dfd/angry_squealing_duck/kicad/breadboard/02_input_buffer.png

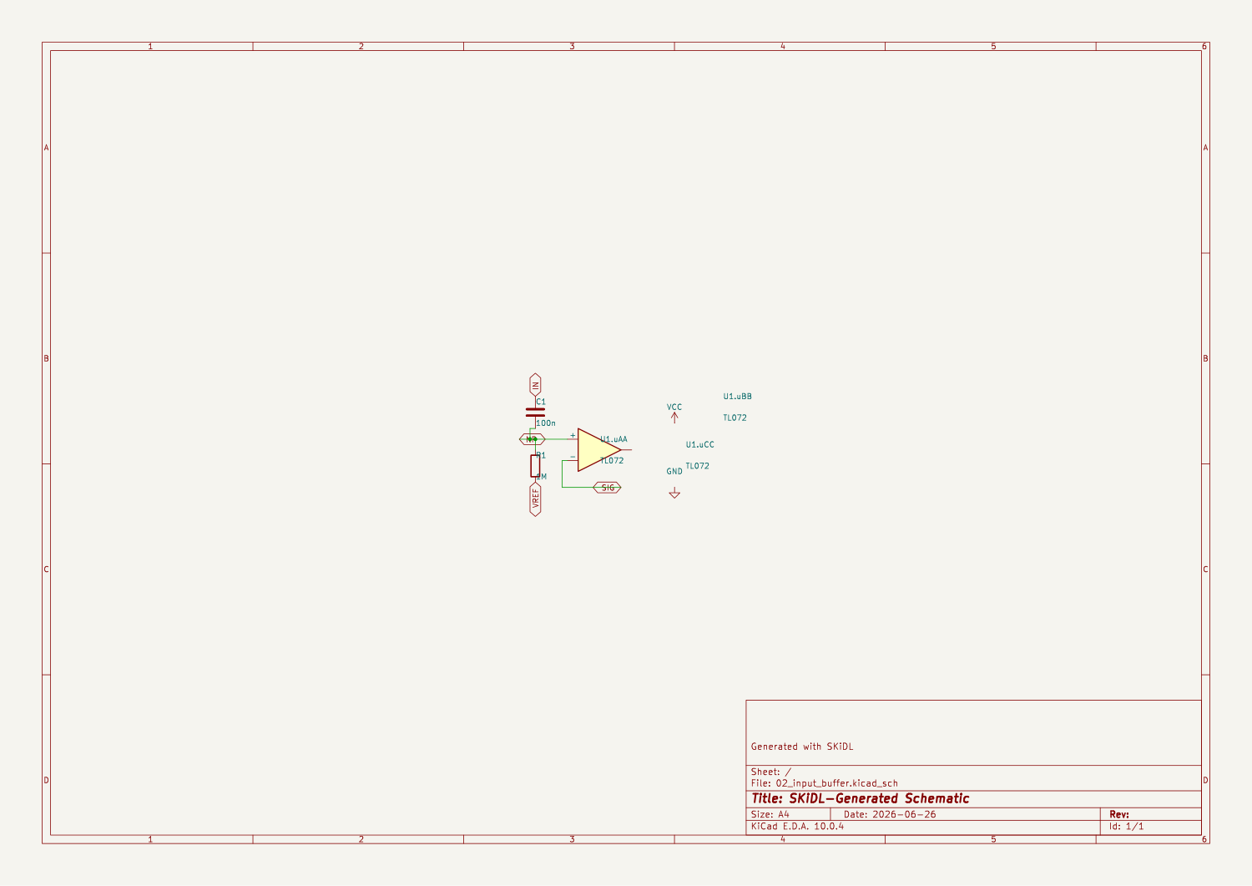
kicad/breadboard/02_input_buffer.png
