dfd/angry_squealing_duck/kicad/breadboard/05_envelope.png

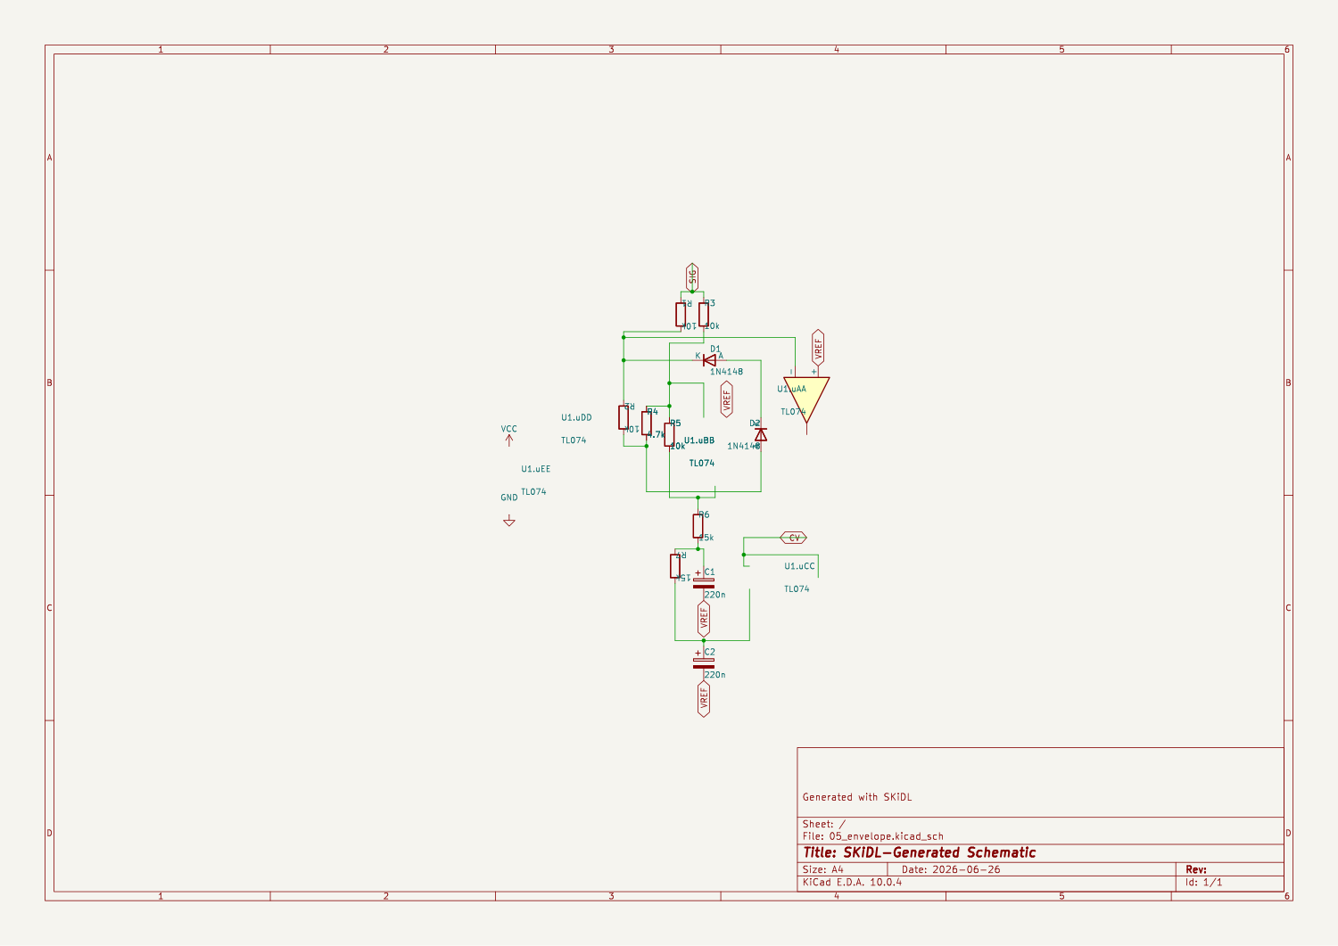
kicad/breadboard/05_envelope.png
