dfd/angry_squealing_duck/kicad/breadboard/06_quack_vtoi.png

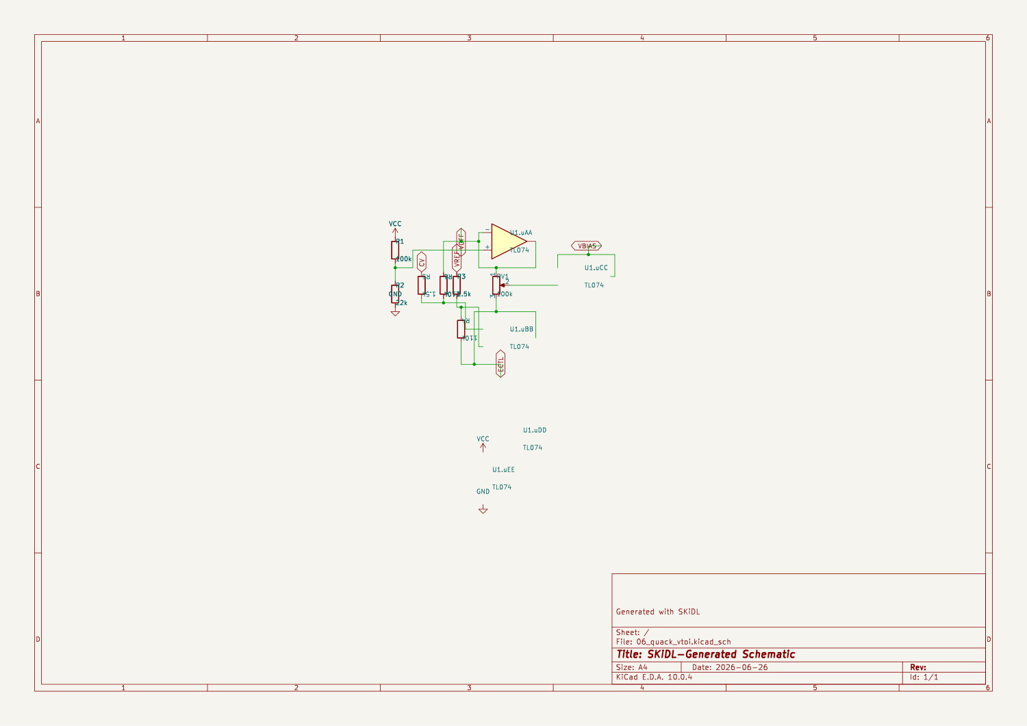
kicad/breadboard/06_quack_vtoi.png
