dfd/angry_squealing_duck/kicad/duck_place.png

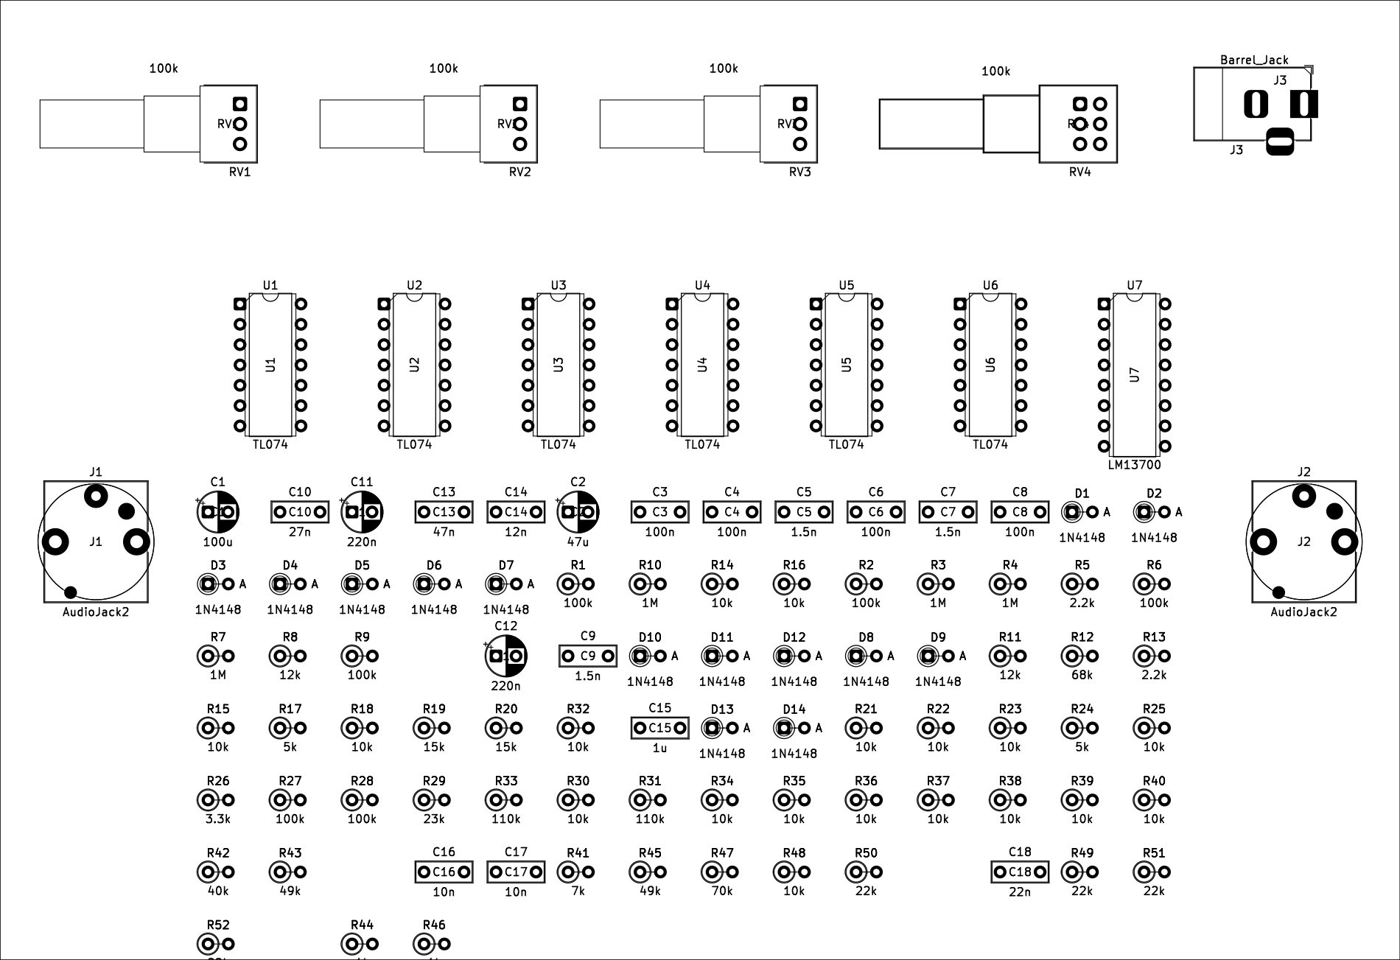
kicad/duck_place.png
