dfd/angry_squealing_duck/spice/blocks/vcf.cir

* ---------------------------------------------------------------------------
* vcf - voltage-controlled state-variable band-pass (Q-Tron core, behavioral)
*
* Pins:  in out gc vref vp vn      params: quack=1
*   gc : GROUND-referenced cutoff control (>=0; 0 = parked). Generated from the
*        envelope by the integration stage (gc = max(cv - vref, 0)).
*
* Chamberlin state-variable loop, band-pass tap:
*   hp = in - lp - d*bp        (all relative to vref)
*   bp = (w0/s) hp             (gm-C integrator 1)
*   lp = (w0/s) bp             (gm-C integrator 2)
* The state-variable loop gives all three responses at once:
*   bp = w0*s/(s^2+d*w0*s+w0^2)  hp = s^2/(...)  lp = w0^2/(...)
* Q-Tron-style mode is a weighted blend of the taps (wlp/wbp/whp), default = BP.
* HP/mixed cut the fundamental below the swept corner -> octave more apparent.
*
* Quack ganged control:
*   - sweep depth (drive): passed to the integrators (w0 swept by gc)
*   - resonance (Q):       Q = 0.7 + 2.8*quack (damping d = 1/Q), so Q ramps
*     LINEARLY 0.7 (CCW, off) -> 3.5 (CW). Linear-in-Q spreads the quack evenly
*     across the knob (vs 1/d which crammed it all at the top and hit Q~10, which
*     buried the octave); 3.5 is a strong-but-musical max that keeps the octave present.
* So Quack CCW = parked, low-Q (effectively off); CW = strong resonant sweep.
* ---------------------------------------------------------------------------
.subckt vcf in out gc vref vp vn params: quack=1 wlp=0 wbp=1 whp=0
* summer -> high-pass state (ideal summing node, referenced to vref)
Bhp hp vref V = (V(in)-V(vref)) - (V(lp)-V(vref)) - (1/(0.7+2.8*quack))*(V(bp)-V(vref))
* two voltage-controlled integrators -> band-pass (bp) and low-pass (lp) taps
Xi1 hp bp gc vref gmint quack={quack}
Xi2 bp lp gc vref gmint quack={quack}
* mode = weighted blend of LP/BP/HP taps (relative to vref)
Bmix mo vref V = wlp*(V(lp)-V(vref)) + wbp*(V(bp)-V(vref)) + whp*(V(hp)-V(vref))
* buffer so downstream loads don't disturb the filter state
Xob mo out out vp vn opamp
.ends vcf
