dfd/angry_squealing_duck/OUT: Pin U1/6/-,-,p7514962063015773255,p6/INPUT, Pin U1/7/,p3768724659903456224,p7/OUTPUT/08_output.kicad_sch

## KiCad design OUT: Pin U1/6/-,-,p7514962063015773255,p6/INPUT, Pin U1/7/,p3768724659903456224,p7/OUTPUT/08_output.kicad_sch (2026-06-26)

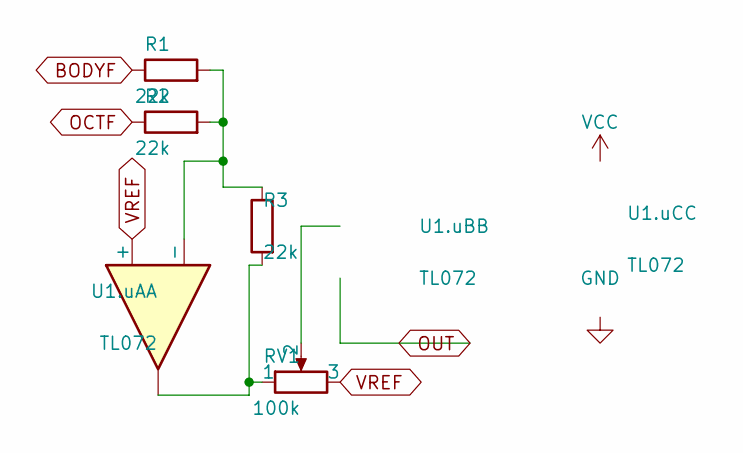
[picture p12: schematic 08_output.kicad_sch]

Parts:
R1, R2, R3: 22k; R_Axial_DIN0207_L6.3mm_D2.5mm_P10.16mm_Horizontal
RV1: 100k
U1.uA, U1.uB, U1.uC: TL072

Connections:
BODYF: R1.1
unnamed: R1.2, R2.2, R3.1, U1.uA.2 (-)
unnamed: R3.2, RV1.1, U1.uA.1
OCTF: R2.1
VREF: RV1.3, U1.uA.3 (+)
